anumby-source/RobotServiceJeunesse2026/img_1.png

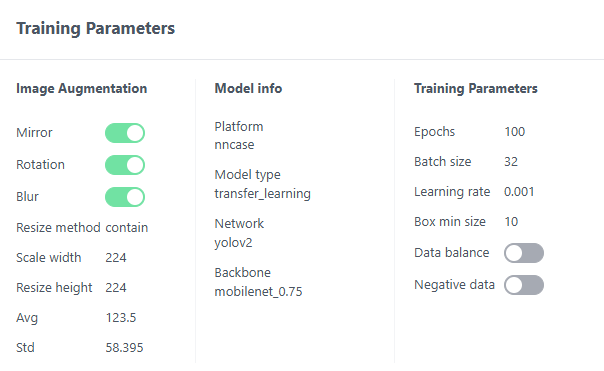
img_1.png
