anumby-source/RobotServiceJeunesse2026/Python/robot.py

###################################################################
#
#   RSJ2026 : Robot code
#
###################################################################

import network
import espnow
from time import sleep_ms, ticks_ms
from machine import Pin, UART
from dcMotor import dcMotor
from mac_addr import *

#
num, _ = find_robot()
robotAddr = robot_mac[num]
telecommandeAddr = telecommande_mac[num]

# motors initialization
ml = dcMotor(pin1=11, pin2=12, pinEn=9)      # left motor
mr = dcMotor(pin1=7, pin2=3, pinEn=5)        # right motor
ml.duty_offset = 0
mr.duty_offset = 0
print("robot : motor init ok")

# led initialization
led = Pin(15, Pin.OUT)
led.off()     # led on
sleep_ms(1000)
led.on()      # led off
print("robot : led init ok")

# UART initialization
u = UART(0, rx=Pin(14, Pin.IN), tx=Pin(13, Pin.OUT))
print("robot : UART init ok")

# espnow initialization
sta = network.WLAN(network.STA_IF) # A WLAN interface must be active
sta.active(True)
sta.disconnect()   # Because ESP8266 auto-connects to last Access Point
print("robot : WLAN init ok")
e = espnow.ESPNow()
e.active(True)
print("robot : espnow init ok")

# essayer de détecter l'adresse de la base via un broadcast espnow
broadcast = b'\xff\xff\xff\xff\xff\xff'

# Ajouter le broadcast comme peer
try:
    e.add_peer(broadcast)
except OSError:
    pass

# -----------------------
# Envoi du broadcast de découverte
# -----------------------
print("Envoi du broadcast HELLO...")
e.send(broadcast, b"HELLO")


# add telecommande to peers
try:
    e.add_peer(telecommandeAddr)
except:
    pass         # if telecommande already in peer list
print(b"robot : telecommande address added", telecommandeAddr)
#


mac_base = None


u.read(u.any())   # empty uart buffer
msg = b''
emsg = b''
old_txt = ""
#
while True:
    # print("wait")
    if u.any():
        msg += u.read(u.any())
        if msg[-1] == 0x0a:  # last char = '\n'
            if mac_base is None:
                pass
            e.send(mac_base, msg)
            print("envoi vers la télécommande", msg)
            e.send(telecommandeAddr, msg)
            msg = b''       

    host, emsg = e.recv(0)
    if host:
        txt = f"on_recv> Reçu de {host} : {emsg}"
        
        if txt != old_txt:
            # print(txt)
            old_text = txt

        if host == telecommandeAddr:
            cmd = emsg
            try:
                # print("on_recv> reçu de la télécommande", cmd)
                exec(cmd)
            except:
                if cmd: print(b"robot : error command:" + cmd)
                led.off()    # led on
        else:
            # base répond avec "MASTER=<MAC>"
            if emsg.startswith(b"MASTER="):
                mac_base = emsg.split(b"=")[1]
                print("MAC de base détecté :", mac_base)

                # Ajouter base comme peer
                try:
                    e.add_peer(mac_base)
                except OSError:
                    pass

                # Envoyer un message de confirmation
                e.send(mac_base, b"READY")
                print("Message READY envoyé à base")
