anumby-source/RobotServiceJeunesse2026/Communication UART K210-ESP32/sender.py

from machine import UART
import time

# setup UART
uart = UART(1, baudrate=115200, tx=5, rx=6)

# loop
i = 0
while True:
    i += 1
    message = 'message from ESP32 #' + f"{i}"
    # n = uart.write(message)
    # print(time.time(),"sent", message, n)
    print("line", uart.readline())

    time.sleep(1)
