anumby-source/RobotServiceJeunesse2026/M5Stack_UnitV/lib_model.py

#labels = ['01', '02', '03', '04', '05', '06', '07']
labels = ['stationnement', 'priorite_a_droite', 'pietons', 'ceder_le_passage', 'limitation_30', 'stop', 'start']
anchors = [0.66, 0.63, 1.44, 1.38, 1.88, 1.91, 1.06, 1.03, 0.88, 0.84]
