anumby-source/RobotServiceJeunesse2026/Python/russhughes/demos/watch.py

""""
watch.py - Analog Watch Display using jpg for the face and filled polygons for the hands
    Requires face_{width}x{height}.jpg in the same directory as this script. See the create_face.py
    script for creating a face image for a given sized display.

    Previous version video: https://youtu.be/NItKb6umMc4
"""

import utime
import math
import st7789
import tft_config


tft = tft_config.config(1)


def hand_polygon(length, radius):
    return [
        (0, 0),
        (-radius, radius),
        (-radius, int(length * 0.3)),
        (-1, length),
        (1, length),
        (radius, int(length * 0.3)),
        (radius, radius),
        (0,0)
    ]


def main():
    '''
    Draw analog watch face and update time
    '''

    # enable display
    tft.init()
    width = tft.width()
    height = tft.height()
    radius = min(width, height)         # face is the smaller of the two
    ofs = (width - radius) // 2         # offset from the left to center the face
    center_x = radius // 2 + ofs - 1    # center of the face horizontally
    center_y = radius // 2 - 1          # center of the face vertically

    # draw the watch face background
    face = "face_{}x{}.jpg".format(width, height)
    tft.jpg(face, 0, 0, st7789.SLOW)

    # create the polygons for the hour, minute and second hands
    # polygons must be closed convex polygons or bad things(tm) happen.

    second_len = int(radius * 0.65 / 2)
    second_poly = hand_polygon(second_len, 2)

    minute_len = int(radius * 0.6 / 2)
    minute_poly = hand_polygon(minute_len, 2)

    hour_len = int(radius * 0.5 / 2)
    hour_poly = hand_polygon(hour_len, 3)

    # constants for calculating hand angles.
    pi_div_6 = math.pi/6
    pi_div_30 = math.pi/30
    pi_div_360 = math.pi/360
    pi_div_1800 = math.pi/1800
    pi_div_2160 = math.pi/2160

    # initialize variables for the bounding rectangles for the
    # hour, minute and second hands. Calling bounding with True will
    # reset the bounds, calling with False will disable bounding

    tft.bounding(True)
    hour_bound = tft.bounding(True)
    minute_bound = tft.bounding(True)
    second_bound = tft.bounding(True)

    while True:
        # save the current time in seconds so we can determine when
        # when to update the display.
        last = utime.time()

        # get the current hour, minute and second
        _, _, _, hour, minute, second, _, _ = utime.localtime()

        # constrain hours to 12 hour time
        hour %= 12

        # calculate the angle of the hour hand in radians
        hour_ang = (
            (hour * pi_div_6) +
            (minute * pi_div_360) +
            (second * pi_div_2160))

        # calculate the angle of the minute hand in radians
        minute_ang = ((minute*pi_div_30)+(second*pi_div_1800))

        # calculate the angle of the second hand on radians
        second_ang = (second*pi_div_30)

        # erase the bounding area of the last drawn hour hand
        x1, y1, x2, y2 = hour_bound
        tft.fill_rect(x1, y1, x2, y2, st7789.WHITE)

        # erase the bounding area of the last drawn minute hand
        x1, y1, x2, y2 = minute_bound
        tft.fill_rect(x1, y1, x2, y2, st7789.WHITE)

        # erase the bounding area of the last drawn second hand
        x1, y1, x2, y2 = second_bound
        tft.fill_rect(x1, y1, x2, y2, st7789.WHITE)

        # draw the hub after erasing the bounding areas to reduce flickering
        tft.fill_circle(center_x, center_y, 5, st7789.BLACK)

        tft.bounding(True)      # clear bounding rectangle

        # draw and fill the hour hand polygon rotated to hour_ang
        tft.fill_polygon(hour_poly, center_x, center_y, st7789.BLACK, hour_ang)

        # get the bounding rectangle of the hour_polygon as drawn and
        # reset the bounding box for the next polygon
        hour_bound = tft.bounding(True, True)

        # draw and fill the minute hand polygon rotated to minute_ang
        tft.fill_polygon(minute_poly, center_x, center_y, st7789.BLACK, minute_ang)

        # get the bounding rectangle of the minute_polygon as drawn and
        # reset the bounding box for the next polygon
        minute_bound = tft.bounding(True, True)

        # draw and fill the second hand polygon rotated to second_ang

        tft.fill_polygon(second_poly, center_x, center_y, st7789.RED, second_ang)

        # get the bounding rectangle of the second_polygon as drawn and
        # reset the bounding box for the next polygon
        second_bound = tft.bounding(True, True)

        # draw the hub again to cover up the second hand
        tft.fill_circle(center_x, center_y, 5, st7789.BLACK)

        # wait until the current second changes
        while last == utime.time():
           utime.sleep_ms(50)

os.chdir('/russhughes/demos')
main()
